StevenKourani/Handheld-Game/Inc/GUI_Icons.h

/*
 * GUI_Icons.h
 *
 *  Created on: Jun 20, 2025
 *      Author: steve
 */

#ifndef INC_GUI_ICONS_H_
#define INC_GUI_ICONS_H_

#include "stm32f4xx_hal.h"
#include "main.h"
#include "ili9341.h"
#include "fonts.h"
#include <string.h>
#include <stdio.h>


void icons(void);
void screen(void);
void icon_border(int);
void icon_select(void);
void icon_buttons(void);

#endif /* INC_GUI_ICONS_H_ */
